matthewgiarra/marantz/2225/P800/3dmodels/molex_5pos_connector_395443005.stp

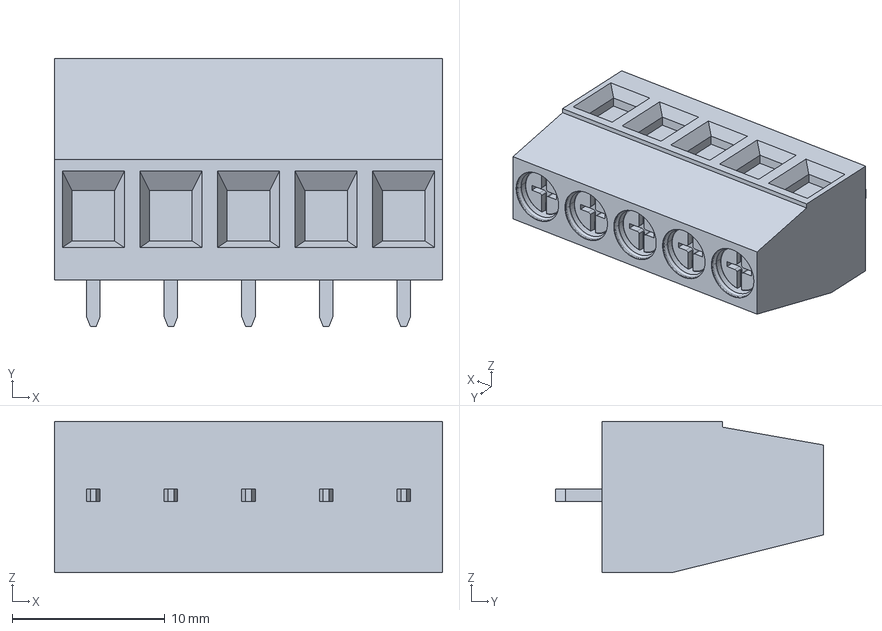
[picture p15: CAD file, 2024-10-03]
2225/P800/3dmodels/molex_5pos_connector_395443005.stp
25.4 x 17.5 x 9.91 mm
