matthewgiarra/marantz/2225/P800/3dmodels/molex_3pos_connector_393570003.stp

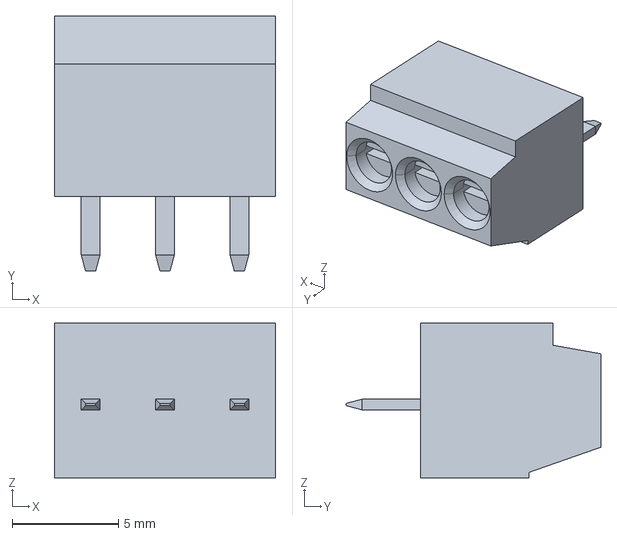
[picture p16: CAD file, 2024-10-03]
2225/P800/3dmodels/molex_3pos_connector_393570003.stp
10.4 x 12.0 x 7.29 mm
