matthewgiarra/marantz/2225/P800/3dmodels/molex_2pos_connector_393570002.stp

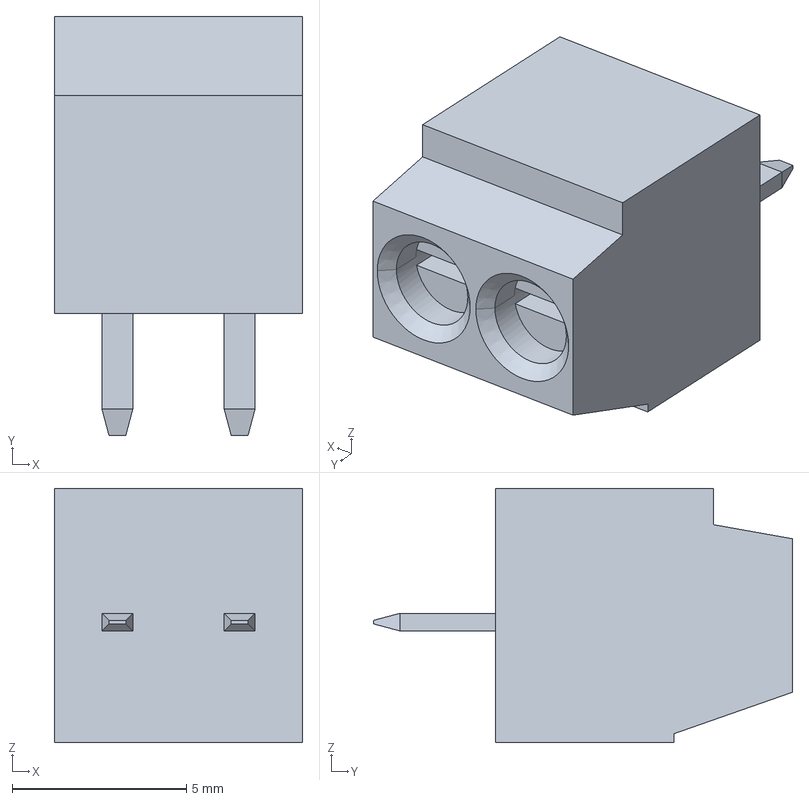
[picture p17: CAD file, 2024-10-03]
2225/P800/3dmodels/molex_2pos_connector_393570002.stp
7.11 x 12.0 x 7.29 mm
